javierbrk/Proyecto-Incubadora-monitoreo/HardWare/modelos3D/humidificador/soporte_sensor_humidificador.stl

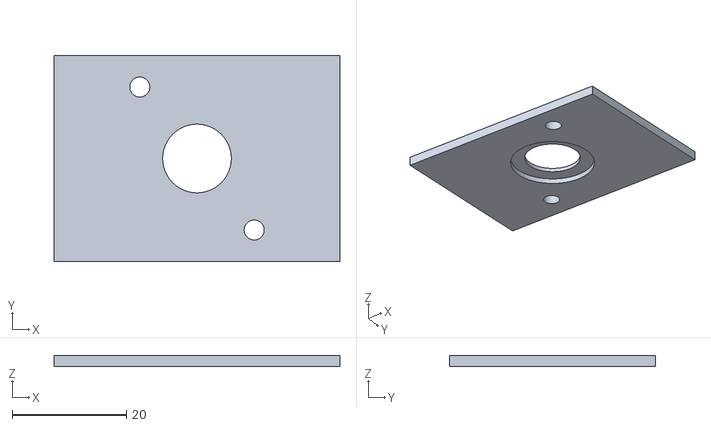
[picture p17: CAD file, 2024-07-10]
HardWare/modelos3D/humidificador/soporte_sensor_humidificador.stl
50.0 x 36.0 x 2.00
