javierbrk/Proyecto-Incubadora-monitoreo/HardWare/modelos3D/SoporteImanTransversal.STL

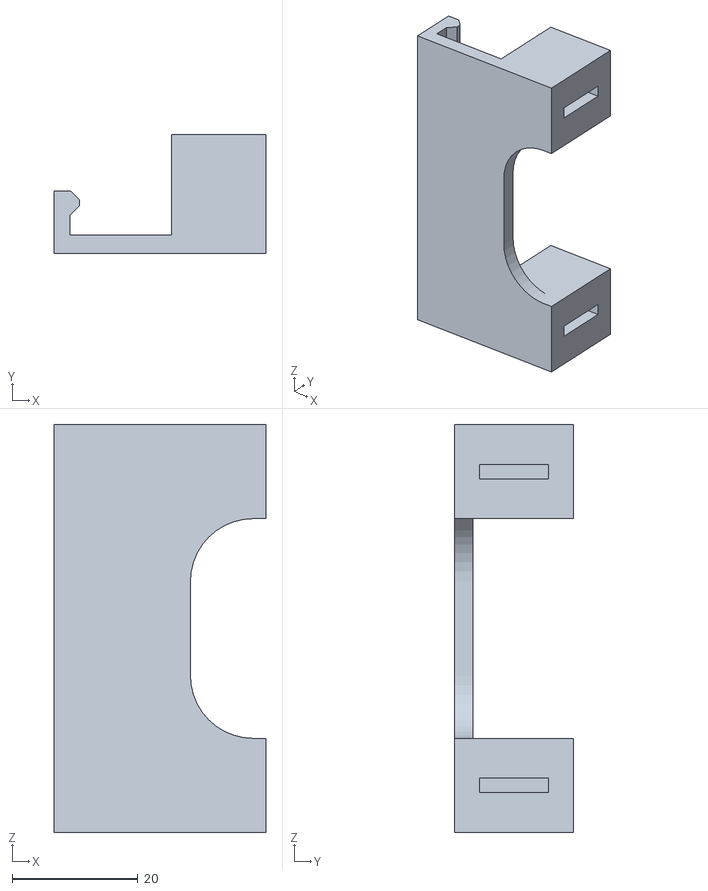
[picture p18: CAD file, 2024-04-19]
HardWare/modelos3D/SoporteImanTransversal.STL
33.7 x 19.0 x 65.0
