javierbrk/Proyecto-Incubadora-monitoreo/HardWare/ModelosMecanica/EnSTEP/SoporteMotorGiraplatoSinPolea.STEP

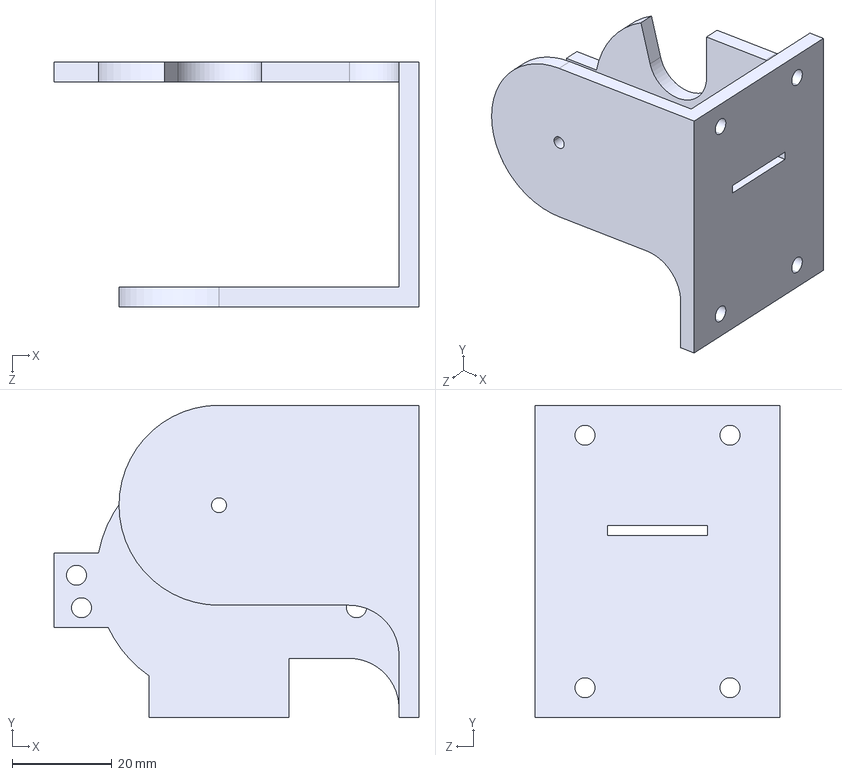
[picture p19: CAD file, 2024-04-19]
HardWare/ModelosMecanica/EnSTEP/SoporteMotorGiraplatoSinPolea.STEP
73.0 x 62.5 x 49.0 mm
