javierbrk/Proyecto-Incubadora-monitoreo/HardWare/modelos3D/CableCanalSoporteReedSwitch.STL

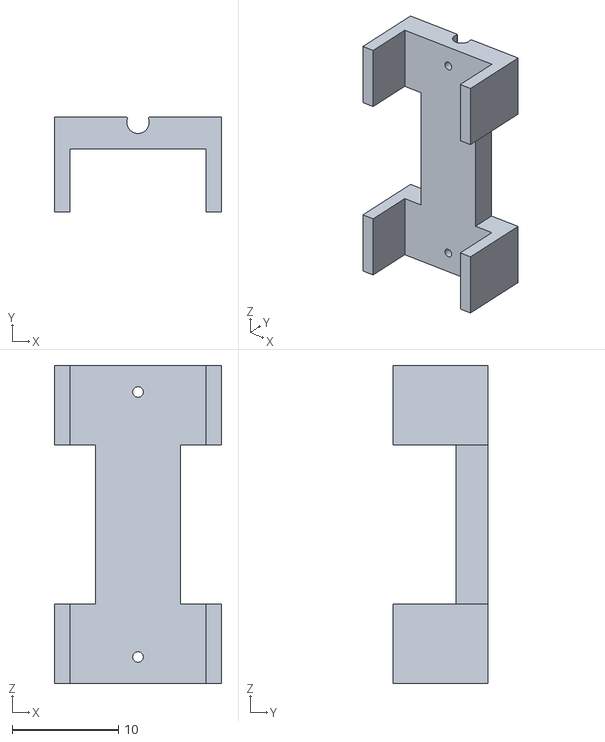
[picture p20: CAD file, 2024-04-19]
HardWare/modelos3D/CableCanalSoporteReedSwitch.STL
15.8 x 8.95 x 30.0
