javierbrk/Proyecto-Incubadora-monitoreo/HardWare/modelos3D/humidificador/Tubo_humidificador.stl

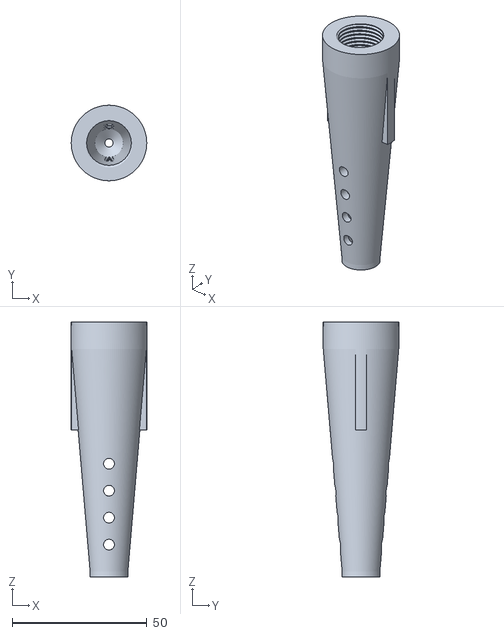
[picture p21: CAD file, 2024-07-10]
HardWare/modelos3D/humidificador/Tubo_humidificador.stl
28.0 x 28.0 x 94.5
