javierbrk/Proyecto-Incubadora-monitoreo/HardWare/ModelosMecanica/EnSTEP/SoporteHumidificador.STEP

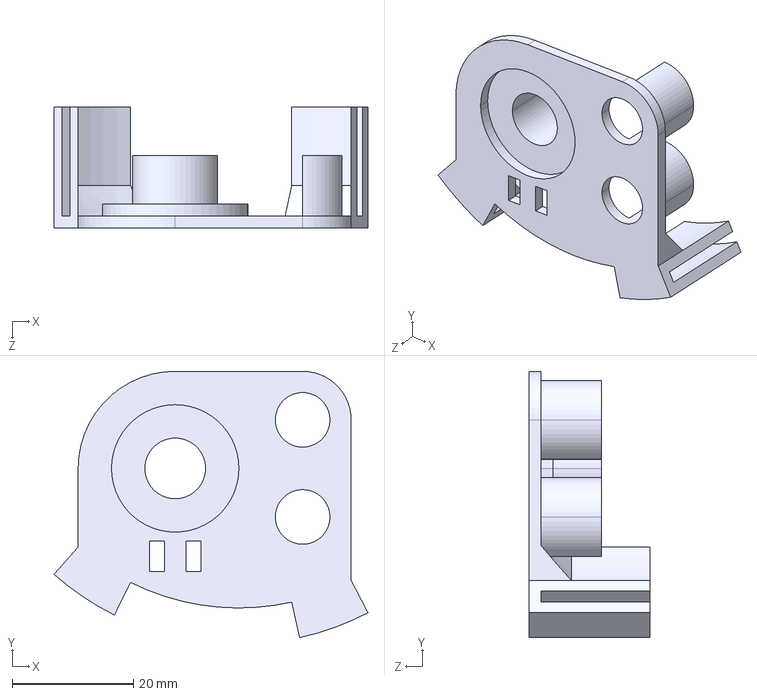
[picture p22: CAD file, 2024-04-19]
HardWare/ModelosMecanica/EnSTEP/SoporteHumidificador.STEP
51.8 x 43.9 x 20.0 mm
