javierbrk/Proyecto-Incubadora-monitoreo/HardWare/ModelosMecanica/EnSTEP/CableCanalSoporteReedSwitch.STEP

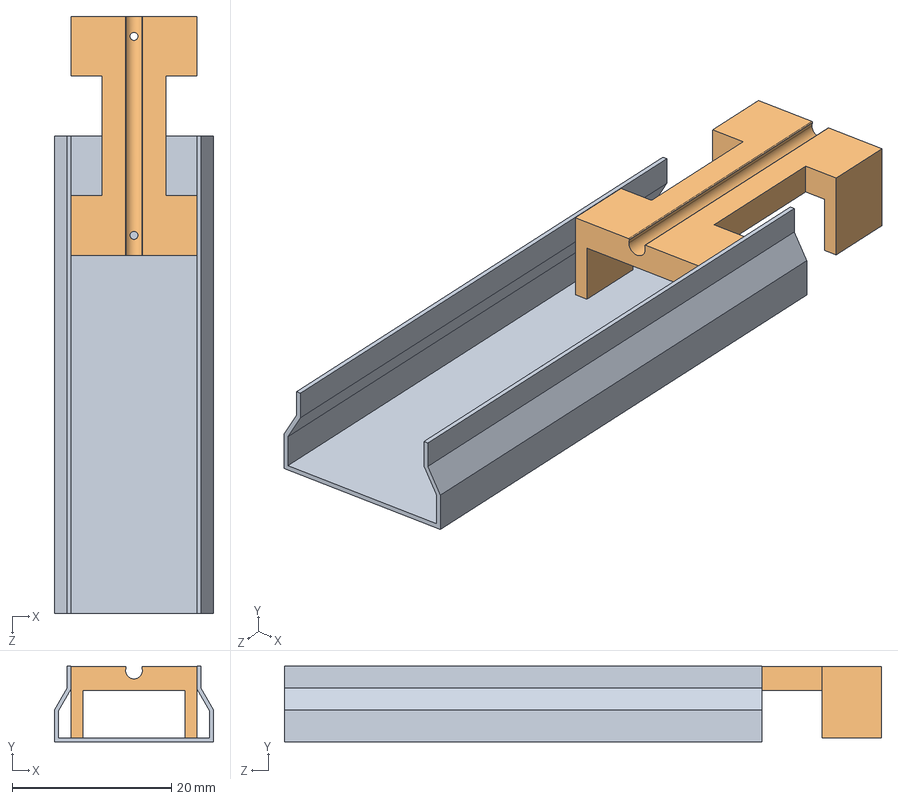
[picture p23: CAD file, 2024-04-19]
HardWare/ModelosMecanica/EnSTEP/CableCanalSoporteReedSwitch.STEP
20.0 x 9.50 x 75.0 mm
