javierbrk/Proyecto-Incubadora-monitoreo/HardWare/modelos3D/FinalCorrea.STL

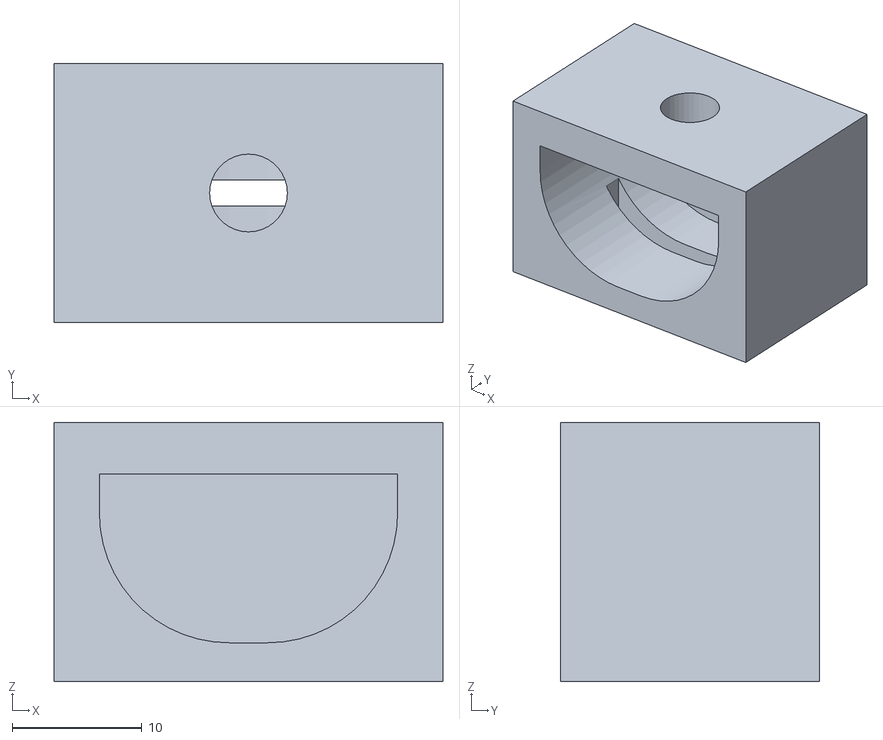
[picture p24: CAD file, 2024-04-19]
HardWare/modelos3D/FinalCorrea.STL
30.0 x 20.0 x 20.0
