javierbrk/Proyecto-Incubadora-monitoreo/HardWare/ModelosMecanica/EnSTEP/PoleaMotorGiraplatoGrande.STEP

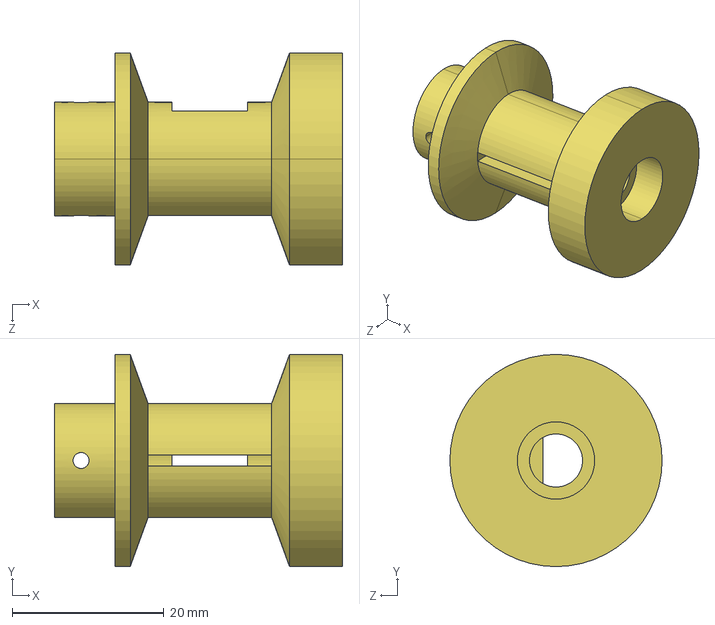
[picture p25: CAD file, 2024-04-19]
HardWare/ModelosMecanica/EnSTEP/PoleaMotorGiraplatoGrande.STEP
38.0 x 28.0 x 28.0 mm
