javierbrk/Proyecto-Incubadora-monitoreo/HardWare/modelos3D/SoporteMotorGiraplatoSinPolea.STL

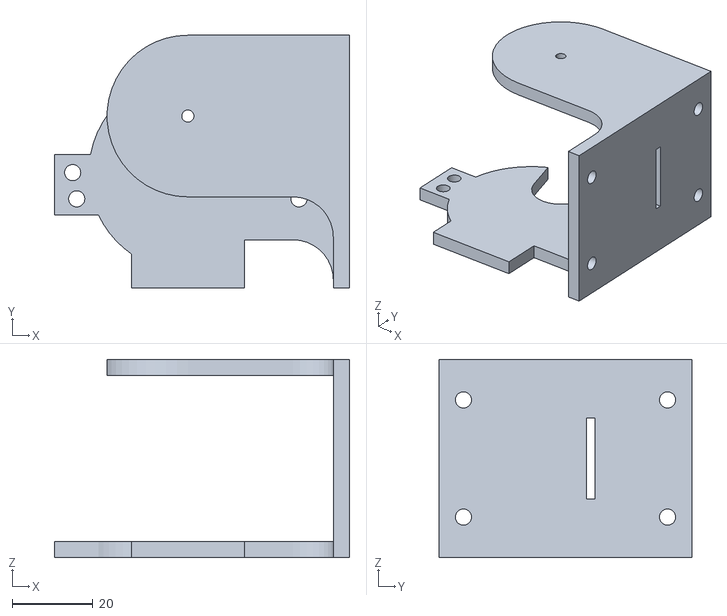
[picture p26: CAD file, 2024-04-19]
HardWare/modelos3D/SoporteMotorGiraplatoSinPolea.STL
73.0 x 62.5 x 49.0
