javierbrk/Proyecto-Incubadora-monitoreo/src/embedded/app/restapi.lua

-- SPDX-FileCopyrightText: 2025 info@altermundi.net
--
-- SPDX-License-Identifier: AGPL-3.0-only

local restapi = {
	incubator = nil,
	configurator = require("configurator"),
	scan_in_progress = false,
	last_request_time = 0,  -- Tiempo de la última solicitud
	min_delay = 1,  -- Delay mínimo entre solicitudes
}

-- Función para forzar el delay entre llamadas
function restapi.forced_delay()
    local current_time = time.get()
    local elapsed = current_time - restapi.last_request_time
    
    if elapsed < restapi.min_delay then
        -- Si no ha pasado suficiente tiempo, retornamos error
		log.addError("wifi", "Forced delay: " .. elapsed .. " < " .. restapi.min_delay)
        return false
    end
    
    -- Actualizamos el tiempo de la última solicitud
    restapi.last_request_time = current_time
    return true
end

-------------------------------------
-- ! @function change config   modify the current config.json file
--
-- !	@param req  		      		server request
-------------------------------------
function restapi.change_config_file(req) 
	local new_config_table = sjson.decode(req.getbody())
	local status = configurator:load_objects_data(new_config_table)

	for param, success in pairs(status) do
		if not success then
			return { status = "400", type = "application/json", body = "Error in setting " .. param }
		end
	end

	local is_file_encoded = configurator:encode_config_file(new_config_table)
	if not is_file_encoded  then
		return { status = "400", type = "application/json", body = "Error in encode_config_file" }
	else
		return { status = "201 Created", type = "application/json", body = "JSON updated and encoded successfully" }
	end
end

-------------------------------------
-- ! @function config_get   get the current config.json parameters
-------------------------------------
function restapi.config_get()
	
	local config_table = configurator:read_config_file()
	local body_json = sjson.encode(config_table)
	if body_json then
		return { status = "200 OK", type = "application/json", body = body_json }
	else
		return { status = "400", type = "application/json", body = "Error config_table not found" }
	end
end

-------------------------------------
-- ! @function actual_ht   get the current humidity and temperature
--
-- !	@param a_temperature get the current temperature
-- !	@param a_humidity		 get the current humidity
-- !	@param a_pressure		 get the current pressure

-------------------------------------
function restapi.actual_ht(a_temperature, a_humidity, a_pressure)
	a_temperature, a_humidity, a_pressure = restapi.incubator.get_values()

	local body_data = {
		errors = log.errors,
		a_temperature = string.format("%.2f", a_temperature),
		a_humidity = string.format("%.2f", a_humidity),
		a_pressure = string.format("%.2f", a_pressure),
		wifi_status = configurator.WiFi.online == 1 and "connected" or "disconnected",
		rotation = restapi.incubator.rotation_enabled 
	}
	
	local body_json = sjson.encode(body_data)
	return { status = "200 OK", type = "application/json", body = body_json }
end

-------------------------------------
--! @function wifi_scan_get   print the current avaliables networks
--
--!	@param req  		      		server request
-------------------------------------
local response_data = {
	message = "error",
	error_message = err
}

function restapi.scan_callback(err, arr)
	restapi.scan_in_progress = false

	if err then
			response_data = {
			message = "error",
			error_message = err
			}
	else
			local networks = {}
			for i, ap in ipairs(arr) do
					local network_info = {
							ssid = ap.ssid,
							rssi = ap.rssi
					}
					table.insert(networks, network_info)
			end
			response_data = {
					message = "success",
					networks = networks
			}
	end
end
	
function restapi.wifi_scan_get(req)
	if not restapi.scan_in_progress then
		restapi.scan_in_progress = true
		wifi.sta.scan({ hidden = 1 }, restapi.scan_callback)
	end
	
	local response_json = sjson.encode(response_data)
	return {
		status = "200 OK",
		type = "application/json",
		body = response_json
	}
end
function restapi.do_rotation(req)
	local can_proceed, error_message = restapi.forced_delay()
    if not can_proceed then
        return { 
            status = "429 Too Many Requests", 
            type = "application/json", 
            body = error_message
        }
    end
	local rotation = sjson.decode(req.getbody())
	if rotation then
		if rotation.move == "up" then
			restapi.incubator.do_rotate_up()
		elseif rotation.move == "down" then
			restapi.incubator.do_rotate_down()
		else
			response_data.message="error"
			return { status = "400", type = "application/json", body = sjson.encode(response_data) }
		end
		stoprotation_tmr= tmr.create()
		stoprotation_tmr:register(1000, tmr.ALARM_SINGLE, restapi.incubator.do_not_rotate)
		stoprotation_tmr:start()
		response_data.message="success"
		return { status = "201", type = "application/json", body = sjson.encode(response_data) }
	else
		response_data.message="error"
		return { status = "400", type = "application/json", body = sjson.encode(response_data) }
	end
end

function restapi.init_module(incubator_object,configurator_object)
	-- * start local server
	restapi.incubator = incubator_object
	restapi.configurator = configurator_object
	
	print("starting server .. fyi maxtemp " .. restapi.incubator.max_temp)
	httpd.start({
		webroot = "web",
		auto_index = httpd.INDEX_ALL
	})

	local function config_get_handler(req)
		local headers = {
			['Access-Control-Allow-Origin'] = '*',
			['Access-Control-Allow-Methods'] = 'GET, POST'
		}

		local config_response = restapi.config_get()
		config_response.headers = headers

		return config_response
	end
	-- * dynamic routes to serve
	httpd.dynamic(httpd.GET, "/config", config_get_handler)
	httpd.dynamic(httpd.POST, "/config", restapi.change_config_file)
	httpd.dynamic(httpd.GET, "/actual", restapi.actual_ht)
	httpd.dynamic(httpd.GET, "/wifi", restapi.wifi_scan_get)
	httpd.dynamic(httpd.POST, "/rotation", restapi.do_rotation)

end

return restapi
