javierbrk/Proyecto-Incubadora-monitoreo/src/embedded/app/ainit.lua

-- SPDX-FileCopyrightText: 2025 info@altermundi.net
--
-- SPDX-License-Identifier: AGPL-3.0-only

--Solo usar en producción 
dofile("credentials.lua")
--dofile("wifiinit.lua")
dofile("incubatorController.lua")
